sish1ka/2-Channel-Mixed-Signal-Data-Acquisition-PCB/LTspice/daq_analog_frontend.asc

C1: cap; 100n
C2: cap; 100n
C3: cap; 1n
D1: diode
R1: res; 1k
R2: res; 16.455k
R3: res; 10k
R4: res; 5.36k
R5: res; 5.36k
R6: res; 47
Rf: res; 5.9k
Rg: res; 10k
U1: UniversalOpAmp2
U2: UniversalOpAmp2
V1: voltage; SINE(2.5 2.5 10); AC 0
V2: voltage; 3.3
V3: voltage; 0
Named nets: 0, V+, V-, Vout
.tran 100m
